atomaly1/serre-auto/code-raspberry/loiCommande.py

##############################################################################################################################
#### Ce fichier python contient les différentes lois de commande permettant de réguler les serres
#### Version 1.0 du 06/01/2024
##############################################################################################################################

listeLois = {"Loi 1","Loi 2"}

#TODO fonction recuperer les données ( temp hum vent) d'un lieu précis


def loiTest():
    print("loi test")
    #pzrvoiéroigvoirrt
